krzychoooo/Mercury_PCB_UOut1-10V_V100/out_0-10V.kicad_sch

## KiCad design out_0-10V.kicad_sch (2025-10-27)

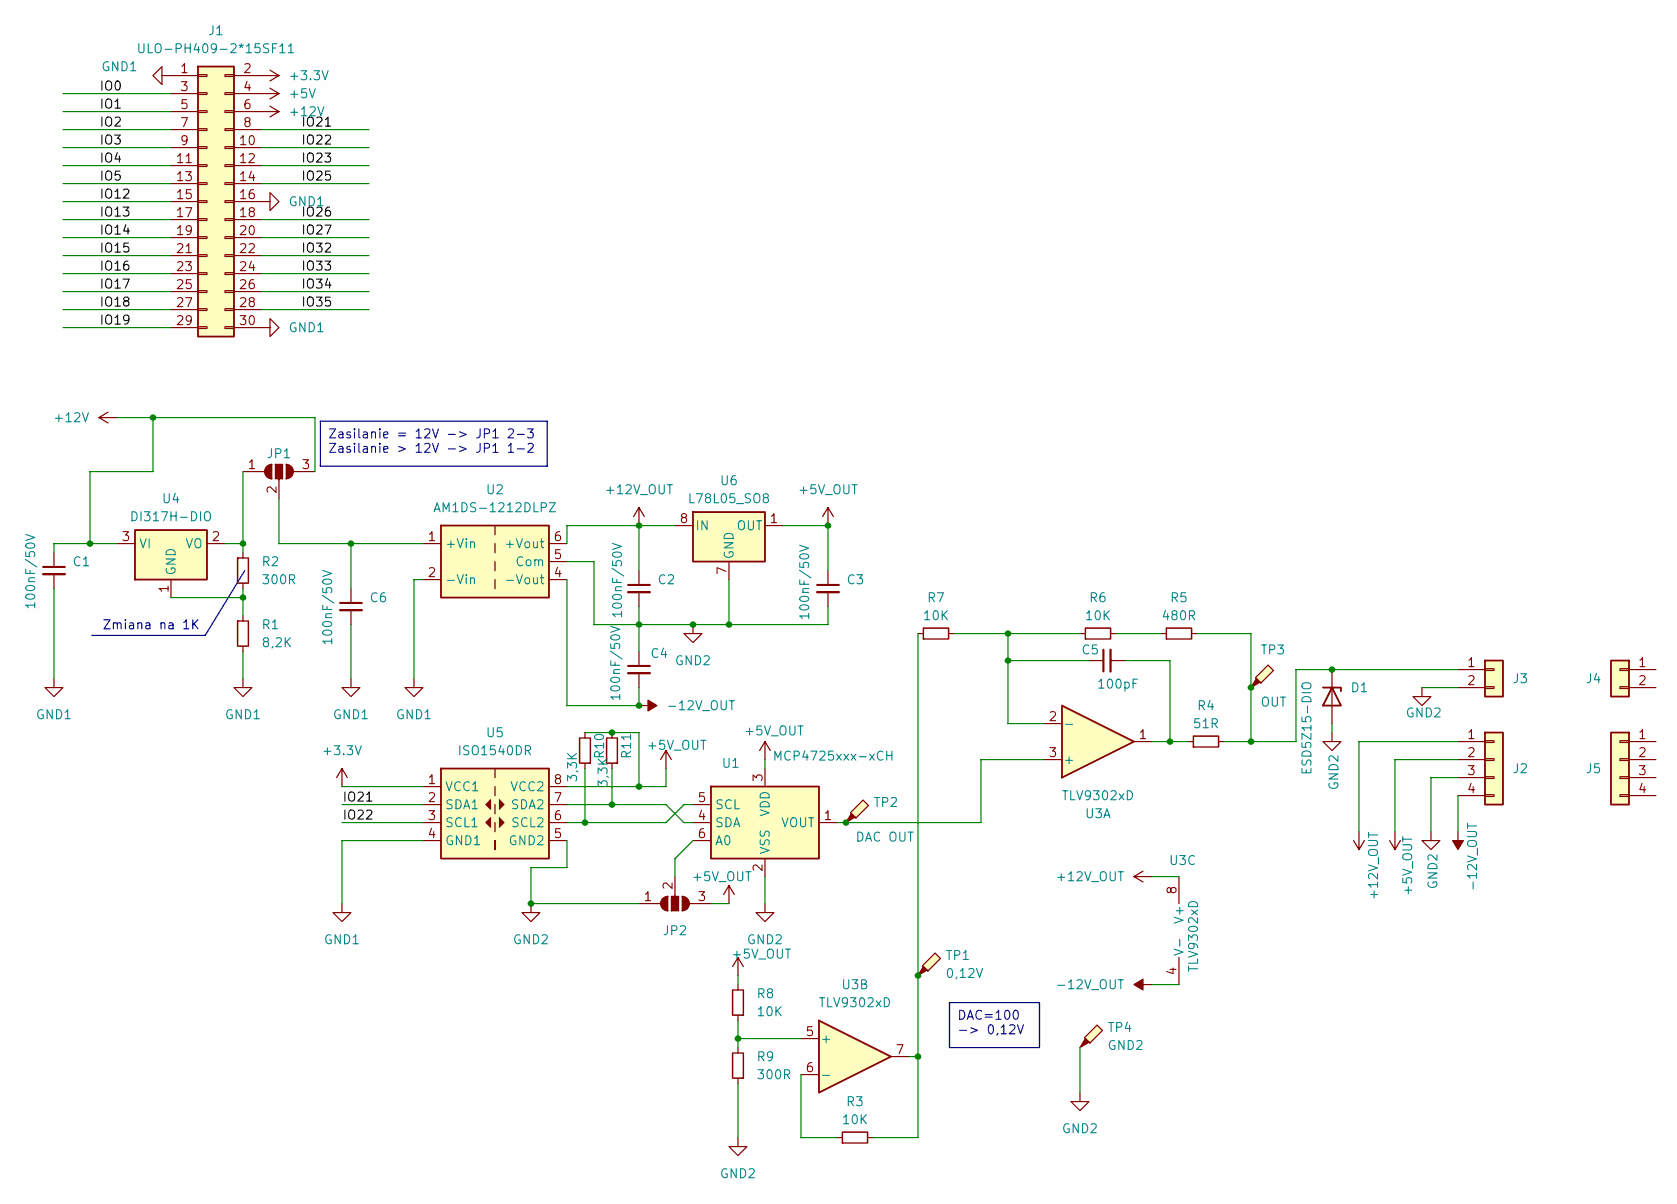
[picture p5: schematic out_0-10V.kicad_sch]

Parts:
C1, C2, C3, C4, C6: 100nF/50V; C_0603_1608Metric
C5: 100pF; C_0603_1608Metric
D1: ESD5Z15-DIO; D_SOD-523
J1: ULO-PH409-2*15SF11; PinHeader_2x15_P2.54mm_Vertical; LCSC part# C132129
J2: OQ0412500000G; 15EDGVC-3.5-04P
J3: 15EDGVC-3.5-02P
J4: 15EDGK-3.5-02P-13; 15EDGVC-3.5-02P
J5: TJ0411530000G; 15EDGVC-3.5-04P
JP1, JP2: SolderJumper_3_Open; SolderJumper-3_P1.3mm_Open_RoundedPad1.0x1.5mm
R1: 8,2K; R_0603_1608Metric
R2, R9: 300R; R_0603_1608Metric
R3, R6, R7, R8: 10K; R_0603_1608Metric
R4: 51R; R_0603_1608Metric
R5: 480R; R_0603_1608Metric
R10, R11: 3,3K; R_0603_1608Metric
TP1: 0,12V; TestPoint_THTPad_1.5x1.5mm_Drill0.7mm
TP2: DAC OUT; TestPoint_THTPad_1.5x1.5mm_Drill0.7mm
TP3: OUT; TestPoint_THTPad_1.5x1.5mm_Drill0.7mm
TP4: GND2; TestPoint_THTPad_1.5x1.5mm_Drill0.7mm
U1: MCP4725xxx-xCH; SOT-23-6
U2: AM1DS-1212DLPZ; Converter_DCDC_TRACO_TBA1-xxxxE_Dual_THT
U3: TLV9302xD; SOIC-8_3.9x4.9mm_P1.27mm
U4: DI317H-DIO; SOT-223-3_TabPin2
U5: ISO1540DR; SOIC-8_3.9x4.9mm_P1.27mm
U6: L78L05_SO8; SOIC-8_3.9x4.9mm_P1.27mm

Connections:
+3.3V: J1.2, U5.1 (VCC1)
+5V: J1.4
+5V_OUT: C3.1, J2.2, JP2.3 (B), R8.2, R10.2, R11.2, U1.3 (VDD), U5.8 (VCC2), U6.1 (OUT)
+12V: C1.1, J1.6, JP1.3 (B), U4.3 (VI)
+12V_OUT: C2.1, J2.1, U2.6 (+Vout), U3.8 (V+), U6.8 (IN)
-12V_OUT: C4.2, J2.4, U2.4 (-Vout), U3.4 (V-)
GND1: C1.2, C6.2, J1.1, J1.16, J1.30, R1.2, U2.2 (-Vin), U5.4 (GND1)
GND2: C2.2, C3.2, C4.1, D1.2 (A), J2.3, J3.2, JP2.1 (A), R9.1, TP4.1, U1.2 (VSS), U2.5 (Com), U5.5 (GND2), U6.2 (GND), U6.3 (GND), U6.6 (GND), U6.7 (GND)
IO0: J1.3
IO1: J1.5
IO2: J1.7
IO3: J1.9
IO4: J1.11
IO5: J1.13
IO12: J1.15
IO13: J1.17
IO14: J1.19
IO15: J1.21
IO16: J1.23
IO17: J1.25
IO18: J1.27
IO19: J1.29
IO21: J1.8, U5.2 (SDA1)
IO22: J1.10, U5.3 (SCL1)
IO23: J1.12
IO25: J1.14
IO26: J1.18
IO27: J1.20
IO32: J1.22
IO33: J1.24
IO34: J1.26
IO35: J1.28
unnamed: C5.1, R6.1, R7.2, U3.2 (-)
unnamed: C5.2, R4.1, U3.1
unnamed: C6.1, JP1.2 (C), U2.1 (+Vin)
unnamed: D1.1 (K), J3.1, R4.2, R5.2, TP3.1
unnamed: JP1.1 (A), R2.1, U4.2 (VO)
unnamed: JP2.2 (C), U1.6 (A0)
unnamed: R1.1, R2.2, U4.1 (GND)
unnamed: R3.1, U3.6 (-)
unnamed: R3.2, R7.1, TP1.1, U3.7
unnamed: R5.1, R6.2
unnamed: R8.1, R9.2, U3.5 (+)
unnamed: R10.1, U1.5 (SCL), U5.6 (SCL2)
unnamed: R11.1, U1.4 (SDA), U5.7 (SDA2)
unnamed: TP2.1, U1.1 (VOUT), U3.3 (+)

Notes on the sheet:
Zasilanie = 12V -> JP1 2-3 Zasilanie > 12V -> JP1 1-2
DAC=100 -> 0,12V
Zmiana na 1K
